samyarsadat/Discrete-SAR-ADC/circuit_diagram/analog_circuit/analog_circuit.kicad_sch

## KiCad design circuit_diagram/analog_circuit/analog_circuit.kicad_sch (2026-08-11)

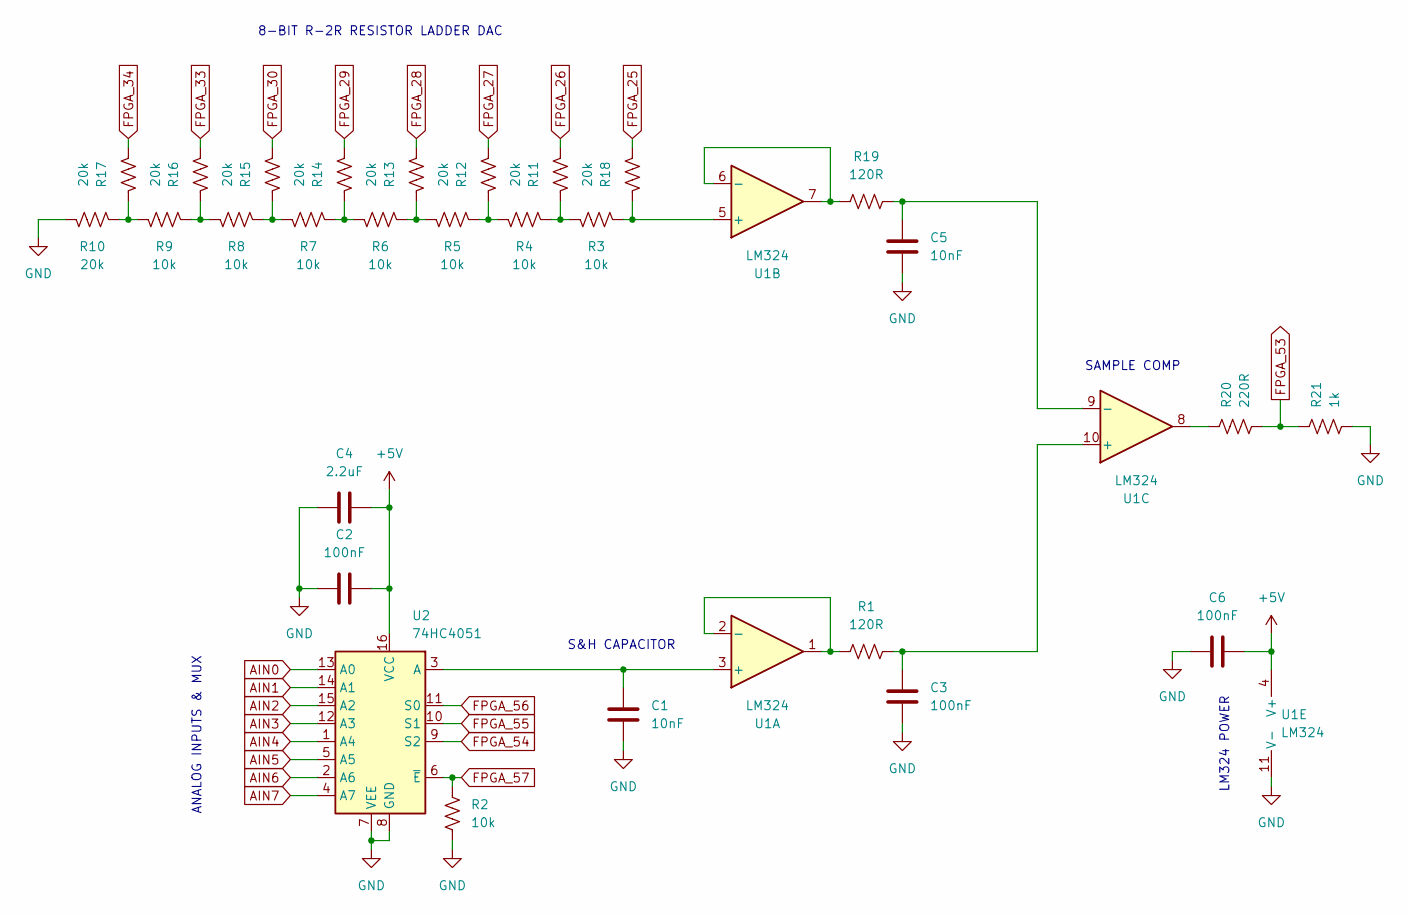
[picture p2: schematic analog_circuit.kicad_sch]

Parts:
C1, C5: 10nF
C2, C3, C6: 100nF
C4: 2.2uF
R1, R19: 120R
R2, R3, R4, R5, R6, R7, R8, R9: 10k
R10, R11, R12, R13, R14, R15, R16, R17, R18: 20k
R20: 220R
R21: 1k
U1: LM324
U2: 74HC4051

Connections:
+5V: C2.2, C4.2, C6.2, U1.4 (V+), U2.16 (VCC)
AIN0: U2.13 (A0)
AIN1: U2.14 (A1)
AIN2: U2.15 (A2)
AIN3: U2.12 (A3)
AIN4: U2.1 (A4)
AIN5: U2.5 (A5)
AIN6: U2.2 (A6)
AIN7: U2.4 (A7)
FPGA_25: R18.2
FPGA_26: R11.2
FPGA_27: R12.2
FPGA_28: R13.2
FPGA_29: R14.2
FPGA_30: R15.2
FPGA_33: R16.2
FPGA_34: R17.2
FPGA_53: R20.1, R21.2
FPGA_54: U2.9 (S2)
FPGA_55: U2.10 (S1)
FPGA_56: U2.11 (S0)
FPGA_57: R2.1, U2.6 (~E)
GND: C1.2, C2.1, C3.2, C4.1, C5.2, C6.1, R2.2, R10.2, R21.1, U1.11 (V-), U2.7 (VEE), U2.8 (GND)
unnamed: C1.1, U1.3 (+), U2.3 (A)
unnamed: C3.1, R1.2, U1.10 (+)
unnamed: C5.1, R19.2, U1.9 (-)
unnamed: R1.1, U1.1, U1.2 (-)
unnamed: R9.2, R10.1, R17.1
unnamed: R3.2, R4.1, R11.1
unnamed: R4.2, R5.1, R12.1
unnamed: R5.2, R6.1, R13.1
unnamed: R6.2, R7.1, R14.1
unnamed: R7.2, R8.1, R15.1
unnamed: R8.2, R9.1, R16.1
unnamed: R3.1, R18.1, U1.5 (+)
unnamed: R19.1, U1.6 (-), U1.7
unnamed: R20.2, U1.8

Notes on the sheet:
S&H CAPACITOR
LM324 POWER
ANALOG INPUTS & MUX
SAMPLE COMP
8-BIT R-2R RESISTOR LADDER DAC
