samyarsadat/Discrete-SAR-ADC/sar_adc_controller/src/i2c_slave/i2cSlave.v

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
`include "i2cSlave_define.v"


module i2cSlave (
  clk,
  rst,
  sda,
  scl,
  
  status_writen,
  status_reg_write_mask,  // R/W
  status_reg_write,       // W
  status_reg_read,        // R
  adc_result_reg,         // R
  sample_clks_reg,        // R/W
  comp_settle_clks_reg,   // R/W
  adc_clken_div_loreg,    // R/W
  adc_clken_div_hireg     // R/W
);

input clk;
input rst;
inout sda;
input scl;
output status_writen;

output [7:0] status_reg_write_mask;
output [7:0] status_reg_write;
input [7:0] status_reg_read;
input [7:0] adc_result_reg;
output [7:0] sample_clks_reg;
output [7:0] comp_settle_clks_reg;
output [7:0] adc_clken_div_loreg;
output [7:0] adc_clken_div_hireg;


// local wires and regs
reg sdaDeb;
reg sclDeb;
reg [`DEB_I2C_LEN-1:0] sdaPipe;
reg [`DEB_I2C_LEN-1:0] sclPipe;

reg [`SCL_DEL_LEN-1:0] sclDelayed;
reg [`SDA_DEL_LEN-1:0] sdaDelayed;
reg [1:0] startStopDetState;
wire clearStartStopDet;
wire sdaOut;
wire sdaIn;
wire [7:0] regAddr;
wire [7:0] dataToRegIF;
wire writeEn;
wire [7:0] dataFromRegIF;
reg [1:0] rstPipe;
wire rstSyncToClk;
reg startEdgeDet;

// detect writes to status register (register 1)
assign status_writen = (regAddr == 1) && writeEn;

assign sda = (sdaOut == 1'b0) ? 1'b0 : 1'bz;
assign sdaIn = sda;

// sync rst rsing edge to clk
always @(posedge clk) begin
  if (rst == 1'b1)
    rstPipe <= 2'b11;
  else
    rstPipe <= {rstPipe[0], 1'b0};
end

assign rstSyncToClk = rstPipe[1];

// debounce sda and scl
always @(posedge clk) begin
  if (rstSyncToClk == 1'b1) begin
    sdaPipe <= {`DEB_I2C_LEN{1'b1}};
    sdaDeb <= 1'b1;
    sclPipe <= {`DEB_I2C_LEN{1'b1}};
    sclDeb <= 1'b1;
  end
  else begin
    sdaPipe <= {sdaPipe[`DEB_I2C_LEN-2:0], sdaIn};
    sclPipe <= {sclPipe[`DEB_I2C_LEN-2:0], scl};
    if (&sclPipe[`DEB_I2C_LEN-1:1] == 1'b1)
      sclDeb <= 1'b1;
    else if (|sclPipe[`DEB_I2C_LEN-1:1] == 1'b0)
      sclDeb <= 1'b0;
    if (&sdaPipe[`DEB_I2C_LEN-1:1] == 1'b1)
      sdaDeb <= 1'b1;
    else if (|sdaPipe[`DEB_I2C_LEN-1:1] == 1'b0)
      sdaDeb <= 1'b0;
  end
end


// delay scl and sda
// sclDelayed is used as a delayed sampling clock
// sdaDelayed is only used for start stop detection
// Because sda hold time from scl falling is 0nS
// sda must be delayed with respect to scl to avoid incorrect
// detection of start/stop at scl falling edge. 
always @(posedge clk) begin
  if (rstSyncToClk == 1'b1) begin
    sclDelayed <= {`SCL_DEL_LEN{1'b1}};
    sdaDelayed <= {`SDA_DEL_LEN{1'b1}};
  end
  else begin
    sclDelayed <= {sclDelayed[`SCL_DEL_LEN-2:0], sclDeb};
    sdaDelayed <= {sdaDelayed[`SDA_DEL_LEN-2:0], sdaDeb};
  end
end

// start stop detection
always @(posedge clk) begin
  if (rstSyncToClk == 1'b1) begin
    startStopDetState <= `NULL_DET;
    startEdgeDet <= 1'b0;
  end
  else begin
    if (sclDeb == 1'b1 && sdaDelayed[`SDA_DEL_LEN-2] == 1'b0 && sdaDelayed[`SDA_DEL_LEN-1] == 1'b1)
      startEdgeDet <= 1'b1;
    else
      startEdgeDet <= 1'b0;
    if (clearStartStopDet == 1'b1)
      startStopDetState <= `NULL_DET;
    else if (sclDeb == 1'b1) begin
      if (sdaDelayed[`SDA_DEL_LEN-2] == 1'b1 && sdaDelayed[`SDA_DEL_LEN-1] == 1'b0) 
        startStopDetState <= `STOP_DET;
      else if (sdaDelayed[`SDA_DEL_LEN-2] == 1'b0 && sdaDelayed[`SDA_DEL_LEN-1] == 1'b1)
        startStopDetState <= `START_DET;
    end
  end
end


registerInterface u_registerInterface(
  .clk(clk),
  .rst(rst),
  .addr(regAddr),
  .dataIn(dataToRegIF),
  .writeEn(writeEn),
  .dataOut(dataFromRegIF),

  .status_reg_write_mask(status_reg_write_mask),
  .status_reg_write(status_reg_write),
  .status_reg_read(status_reg_read),
  .adc_result_reg(adc_result_reg),
  .sample_clks_reg(sample_clks_reg),
  .comp_settle_clks_reg(comp_settle_clks_reg),
  .adc_clken_div_loreg(adc_clken_div_loreg),
  .adc_clken_div_hireg(adc_clken_div_hireg)
);

serialInterface u_serialInterface (
  .clk(clk), 
  .rst(rstSyncToClk | startEdgeDet), 
  .dataIn(dataFromRegIF), 
  .dataOut(dataToRegIF), 
  .writeEn(writeEn),
  .regAddr(regAddr), 
  .scl(sclDelayed[`SCL_DEL_LEN-1]), 
  .sdaIn(sdaDeb), 
  .sdaOut(sdaOut), 
  .startStopDetState(startStopDetState),
  .clearStartStopDet(clearStartStopDet) 
);


endmodule


 
